zsellera/openstint-preamp/docs/amplifier.asc

C1: cap; 100n
C2: cap; 100n
C3: cap; 470p
C4: cap; 12p
C6: cap; 1.8n
C7: cap; 470p
L2: ind; 2.2µ
L3: ind; 1n
L4: ind; 560n
L5: ind; 2.2µ
Q1: npn; 2N2369
R1: res; 49
R2: res; 4.7
R3: res; 820
R4: res; 470
R5: res; 150
R6: res; 50
V1: voltage; 3.2
V2: voltage; SINE(0 0.001 5meg); AC 1; Rser=50
Named nets: 0, out
.ac dec 100 1meg 29meg
.net I(R6) V2
.tran 0 100u 0 1n
.options numdgt = 7
.options plotwinsize = 0
.step param ampl list 100u 1m 10m 100m
.four 5meg v(out)
.tran 10u
.op
