zsellera/openstint-preamp/docs/bias-tee.asc

C1: cap; 3.3µ; Rser=4.2m Lser=300p mfg="Würth Elektronik" pn="885012107008 WCAP-CSGP 0805" type="X5R"
C2: cap; 3.3µ; Rser=4.2m Lser=300p mfg="Würth Elektronik" pn="885012107008 WCAP-CSGP 0805" type="X5R"
C3: cap; 3.3µ; Rser=4.2m Lser=300p mfg="Würth Elektronik" pn="885012107008 WCAP-CSGP 0805" type="X5R"
C4: cap; 3.3µ; Rser=4.2m Lser=300p mfg="Würth Elektronik" pn="885012107008 WCAP-CSGP 0805" type="X5R"
L1: ind; 10µ; Ipk=830m Rser=380m Rpar=infin. Cpar=0 mfg="Murata" pn="LQH2HPN100MJRL"
L2: FerriteBead; 1µ; Ipk=1.5 Rser=90m Rpar=636 Cpar=836f mfg="Würth Elektronik" pn="74269262601 WE-TMSB 0603"
V1: voltage; ""; AC 1
Named nets: 0
.ac dec 100 1k 1000meg
